uriba107/deduino/pcb/eyebrows - referance schematic/Glareshield-revA.sch

## EAGLE design pcb/eyebrows - referance schematic/Glareshield-revA.sch (2015-08-18)

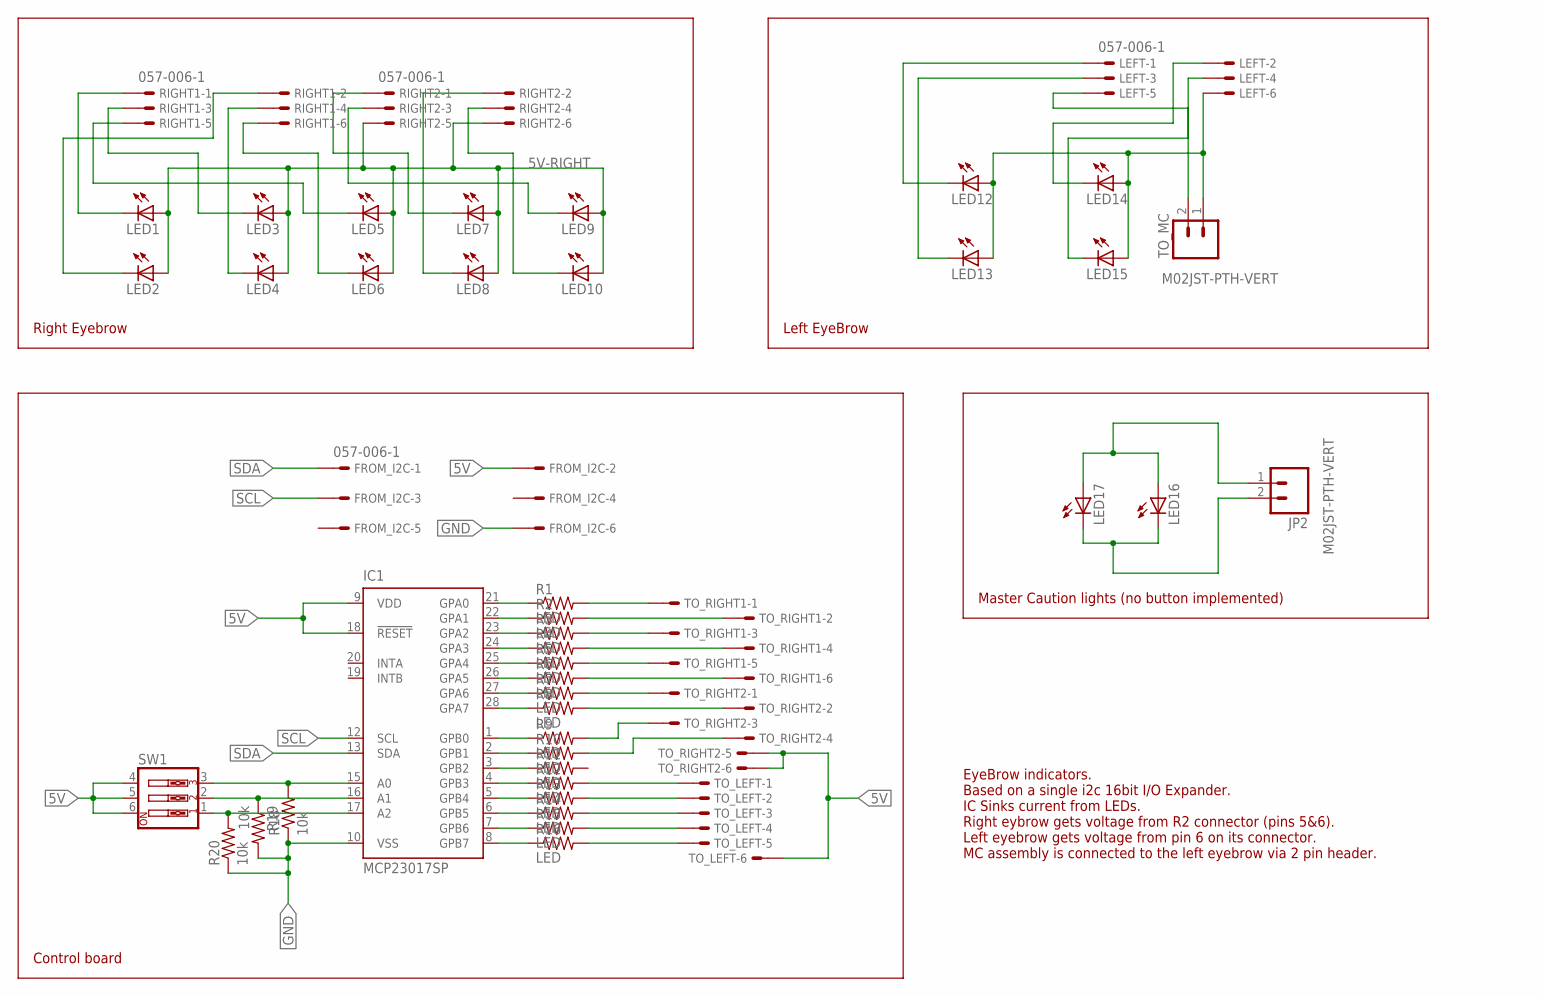
[picture p23: schematic Glareshield-revA.sch]

Parts:
FROM_I2C: 057-006-1
IC1: MCP23017SP; DIL28-3
JP2: M02JST-PTH-VERT; JST-2-PTH-VERT
LED1, LED2, LED3, LED4, LED5, LED6, LED7, LED8, LED9, LED10, LED12, LED13, LED14, LED15, LED16, LED17: LED3MM
LEFT: 057-006-1
R1, R2, R3, R4, R5, R6, R7, R8, R9, R10, R11, R12, R13, R14, R15, R16: LED; 0204/7
R18, R19, R20: 10k; 0204/7
RIGHT1, RIGHT2: 057-006-1
SW1: SW_DIP-3; EDG-03
TO_LEFT: 057-006-1
TO_MC: M02JST-PTH-VERT; JST-2-PTH-VERT
TO_RIGHT1, TO_RIGHT2: 057-006-1

Connections:
5V: FROM_I2C.2, IC1.9 (VDD), IC1.18 (!RESET), SW1.4, SW1.5, SW1.6, TO_LEFT.6, TO_RIGHT2.5, TO_RIGHT2.6
5V-LEFT: LED12.A, LED13.A, LED14.A, LED15.A, LEFT.6, TO_MC.1
5V-RIGHT: LED1.A, LED2.A, LED3.A, LED4.A, LED5.A, LED6.A, LED7.A, LED8.A, LED9.A, LED10.A, RIGHT2.5, RIGHT2.6
GND: FROM_I2C.6, IC1.10 (VSS), R18.1, R19.2, R20.1
unnamed: IC1.24 (GPA3), R4.1
unnamed: IC1.21 (GPA0), R1.1
unnamed: IC1.22 (GPA1), R2.1
unnamed: IC1.23 (GPA2), R3.1
unnamed: IC1.25 (GPA4), R5.1
unnamed: IC1.26 (GPA5), R6.1
unnamed: IC1.27 (GPA6), R7.1
unnamed: IC1.28 (GPA7), R8.1
unnamed: IC1.1 (GPB0), R9.1
unnamed: IC1.2 (GPB1), R10.1
unnamed: IC1.3 (GPB2), R11.1
unnamed: IC1.4 (GPB3), R12.1
unnamed: IC1.5 (GPB4), R13.1
unnamed: IC1.6 (GPB5), R14.1
unnamed: IC1.7 (GPB6), R15.1
unnamed: IC1.8 (GPB7), R16.1
unnamed: LED1.K (C), RIGHT1.1
unnamed: LED3.K (C), RIGHT1.3
unnamed: LED5.K (C), RIGHT1.5
unnamed: LED6.K (C), RIGHT1.6
unnamed: LED4.K (C), RIGHT1.4
unnamed: LED2.K (C), RIGHT1.2
unnamed: LED7.K (C), RIGHT2.1
unnamed: R12.2, TO_LEFT.1
unnamed: LED9.K (C), RIGHT2.3
unnamed: LED8.K (C), RIGHT2.2
unnamed: LED10.K (C), RIGHT2.4
unnamed: R1.2, TO_RIGHT1.1
unnamed: R2.2, TO_RIGHT1.2
unnamed: R3.2, TO_RIGHT1.3
unnamed: R4.2, TO_RIGHT1.4
unnamed: R5.2, TO_RIGHT1.5
unnamed: R6.2, TO_RIGHT1.6
unnamed: R7.2, TO_RIGHT2.1
unnamed: R8.2, TO_RIGHT2.2
unnamed: R10.2, TO_RIGHT2.4
unnamed: R9.2, TO_RIGHT2.3
unnamed: IC1.17 (A2), R20.2, SW1.1
unnamed: IC1.16 (A1), R19.1, SW1.2
unnamed: IC1.15 (A0), R18.2, SW1.3
unnamed: LED12.K (C), LEFT.1
unnamed: R13.2, TO_LEFT.2
unnamed: R14.2, TO_LEFT.3
unnamed: R15.2, TO_LEFT.4
unnamed: R16.2, TO_LEFT.5
unnamed: LEFT.5, TO_MC.2
unnamed: LED13.K (C), LEFT.3
unnamed: LED14.K (C), LEFT.2
unnamed: LED15.K (C), LEFT.4
unnamed: JP2.1, LED16.A, LED17.A
unnamed: JP2.2, LED16.K (C), LED17.K (C)
SCL: FROM_I2C.3, IC1.12 (SCL)
SDA: FROM_I2C.1, IC1.13 (SDA)

Notes on the sheet:
Control board
Right Eyebrow
Left EyeBrow
Master Caution lights (no button implemented)
EyeBrow indicators. Based on a single i2c 16bit I/O Expander. IC Sinks current from LEDs. Right eybrow gets voltage from R2 connector (pins 5&6). Left eyebrow gets voltage from pin 6 on its connector. MC assembly is connected to the left eyebrow via 2 pin header.
