uriba107/deduino/arduino_code/DEDunio_arduino/falconded_moon_u8g.h

/*
  Fontname: -FontForge-FalconDED_MoonVP-Book-R-Normal--16-160-72-72-P-99-WinRoman-0
  Copyright: Copyright MoonVP 2015 cloned from FalconDED wide by "alancoolhand" and "uri_ba"
  Capital A Height: 10, '1' Height: 10
  Calculated Max Values w=10 h=12 x= 5 y= 6 dx=10 dy= 0 ascent=11 len=24
  Font Bounding box     w=10 h=12 x= 0 y=-1
  Calculated Min Values           x= 0 y=-1 dx= 0 dy= 0
  Pure Font   ascent =10 descent=-1
  X Font      ascent =10 descent=-1
  Max Font    ascent =11 descent=-1
*/
//#include "u8g.h"
const u8g_fntpgm_uint8_t FalconDED_wide[3118] U8G_FONT_SECTION("FalconDED_wide") = {
  0,10,12,0,255,10,1,232,3,203,32,255,255,11,255,10,
  255,0,0,0,10,0,1,2,10,10,10,4,0,192,192,192,
  192,192,192,192,0,192,192,6,4,4,10,2,6,204,204,68,
  136,8,10,10,10,1,0,102,102,255,255,102,102,255,255,102,
  102,8,10,10,10,1,0,24,126,219,216,254,127,27,219,126,
  24,8,10,10,10,1,0,225,163,231,14,28,56,112,231,197,
  135,8,10,10,10,1,0,60,126,96,112,59,127,198,198,255,
  115,2,4,4,10,4,6,192,192,64,128,4,10,10,10,3,
  0,48,96,192,192,192,192,192,192,96,48,4,10,10,10,3,
  0,192,96,48,48,48,48,48,48,96,192,7,9,9,10,2,
  0,16,146,84,56,254,56,84,146,16,8,8,8,10,1,1,
  24,24,24,255,255,24,24,24,2,4,4,10,5,0,192,192,
  64,128,8,2,2,10,1,4,255,255,2,2,2,10,4,0,
  192,192,8,10,10,10,1,0,1,3,7,14,28,56,112,224,
  192,128,8,10,10,10,1,0,60,126,231,195,195,195,195,231,
  126,60,6,10,10,10,2,0,48,112,240,48,48,48,48,48,
  252,252,8,10,10,10,1,0,126,255,195,3,31,126,240,192,
  255,255,8,10,10,10,1,0,255,255,14,28,62,7,3,195,
  255,126,8,10,10,10,1,0,204,204,204,204,204,255,255,12,
  12,12,8,10,10,10,1,0,255,255,192,192,254,255,3,195,
  255,126,8,10,10,10,1,0,126,254,192,192,254,255,195,195,
  255,126,8,10,10,10,1,0,255,255,3,7,14,28,56,112,
  96,96,8,10,10,10,1,0,126,255,195,195,126,255,195,195,
  255,126,8,10,10,10,1,0,126,255,195,195,255,127,3,3,
  127,126,2,6,6,10,4,2,192,192,0,0,192,192,2,8,
  8,10,4,0,192,192,0,0,192,192,64,128,7,10,10,10,
  2,0,14,28,56,112,224,224,112,56,28,14,6,6,6,10,
  2,2,252,252,0,0,252,252,7,10,10,10,2,0,224,112,
  56,28,14,14,28,56,112,224,8,10,10,10,1,0,126,255,
  195,3,7,30,24,0,24,24,8,10,10,10,1,0,24,60,
  126,255,0,0,255,126,60,24,8,10,10,10,1,0,24,60,
  126,231,195,195,255,255,195,195,8,10,10,10,1,0,254,255,
  195,195,254,254,195,195,255,254,8,10,10,10,1,0,126,255,
  195,192,192,192,192,195,255,126,8,10,10,10,1,0,254,255,
  99,99,99,99,99,99,255,254,8,10,10,10,1,0,255,255,
  192,192,248,248,192,192,255,255,8,10,10,10,1,0,255,255,
  192,192,248,248,192,192,192,192,8,10,10,10,1,0,126,255,
  195,192,207,207,195,195,255,127,8,10,10,10,1,0,195,195,
  195,195,255,255,195,195,195,195,8,10,10,10,1,0,255,255,
  24,24,24,24,24,24,255,255,7,10,10,10,1,0,126,126,
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
