uriba107/deduino/arduino_code/DEDunio_arduino/falconded_full_u8g.h

/*
  Fontname: -FreeType-FalconDED-Medium-R-Normal--17-120-100-100-P-71-ISO10646-1
  Copyright: Copyright uri_ba 2014
  Capital A Height: 9, '1' Height: 9
  Calculated Max Values w= 9 h=11 x= 3 y= 5 dx= 9 dy= 0 ascent=10 len=22
  Font Bounding box     w= 9 h=11 x= 0 y=-1
  Calculated Min Values           x= 0 y=-1 dx= 0 dy= 0
  Pure Font   ascent = 9 descent=-1
  X Font      ascent = 9 descent=-1
  Max Font    ascent =10 descent=-1
*/

const u8g_fntpgm_uint8_t FalconDED_full[2190] U8G_FONT_SECTION("FalconDED_full") = {
  0,9,11,0,255,9,1,197,3,138,32,255,255,10,255,9,
  255,0,0,0,8,0,0,2,9,9,6,3,255,192,192,192,
  192,192,192,0,192,192,5,3,3,8,2,5,216,216,216,6,
  9,9,8,1,255,72,72,252,72,72,72,252,72,72,6,9,
  9,8,1,255,48,120,180,176,120,52,180,120,48,6,9,9,
  8,1,255,68,172,72,16,48,32,72,212,136,6,9,9,8,
  1,255,48,120,72,48,120,204,220,248,116,1,3,3,4,2,
  5,128,128,128,4,9,9,7,2,255,48,96,192,192,192,192,
  192,96,48,4,9,9,7,2,255,192,96,48,48,48,48,48,
  96,192,7,7,7,9,1,1,16,84,56,254,56,84,16,6,
  6,6,8,1,1,48,48,252,252,48,48,3,4,4,6,2,
  0,96,96,192,192,6,2,2,8,1,3,252,252,2,2,2,
  6,3,0,192,192,6,9,9,8,1,255,4,12,8,16,48,
  32,64,192,128,6,9,9,8,1,255,48,120,204,204,204,204,
  204,120,48,4,9,9,7,2,255,32,96,224,96,96,96,96,
  240,240,6,9,9,8,1,255,120,252,204,12,60,120,192,252,
  252,6,9,9,8,1,255,252,252,12,24,56,12,204,252,120,
  6,9,9,8,1,255,216,216,216,216,252,252,24,24,24,6,
  9,9,8,1,255,252,252,192,248,252,12,204,252,120,6,9,
  9,8,1,255,124,252,192,248,252,204,204,252,120,6,9,9,
  8,1,255,252,252,12,12,24,48,96,96,96,6,9,9,8,
  1,255,120,252,204,252,120,204,204,252,120,6,9,9,8,1,
  255,120,252,204,204,252,124,12,124,120,2,6,6,5,2,2,
  192,192,0,0,192,192,3,7,7,5,1,0,96,96,0,96,
  96,192,192,4,6,6,7,2,1,48,96,192,192,96,48,4,
  6,6,7,2,1,240,240,0,0,240,240,4,6,6,7,2,
  1,192,96,48,48,96,192,6,9,9,8,1,255,120,252,204,
  24,24,48,0,48,48,6,9,9,8,1,255,48,120,252,0,
  0,0,252,120,48,6,9,9,8,1,255,48,120,252,204,204,
  252,252,204,204,6,9,9,8,1,255,248,252,204,248,248,204,
  204,252,248,6,9,9,8,1,255,120,204,204,192,192,192,204,
  204,120,6,9,9,8,1,255,248,108,108,108,108,108,108,108,
  248,6,9,9,8,1,255,252,252,192,248,248,192,192,252,252,
  6,9,9,8,1,255,252,252,192,248,248,192,192,192,192,6,
  9,9,8,1,255,120,252,192,192,220,220,204,252,120,6,9,
  9,8,1,255,204,204,204,252,252,204,204,204,204,6,9,9,
  8,1,255,252,252,48,48,48,48,48,252,252,6,9,9,8,
  1,255,252,252,48,48,48,48,48,240,224,6,9,9,8,1,
  255,204,220,248,224,192,224,240,220,204,6,9,9,8,1,255,
  192,192,192,192,192,192,192,252,252,6,9,9,8,1,255,132,
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
  
