uriba107/deduino/arduino_code/DEDunio_arduino/fuelflow_u8g.h

/*
  Fontname: -FontForge-MS 33558-Book-R-Normal--26-260-72-72-P-201-ISO10646-1
  Copyright: (c) 2000 Derek Higgs
  Capital A Height: 0, '1' Height: 25
  Calculated Max Values w=19 h=26 x= 6 y= 1 dx=26 dy= 0 ascent=26 len=78
  Font Bounding box     w=20 h=26 x= 0 y= 0
  Calculated Min Values           x= 0 y= 0 dx= 0 dy= 0
  Pure Font   ascent =25 descent= 0
  X Font      ascent =25 descent= 0
  Max Font    ascent =26 descent= 0
*/
//#include "u8g.h"
const u8g_fntpgm_uint8_t fuelflow_u8g[1122] U8G_FONT_SECTION("fuelflow_u8g") = {
  0,20,26,0,0,25,2,195,3,195,32,255,0,26,0,25,
  0,0,0,0,26,0,1,255,255,255,255,255,255,255,255,255,
  255,255,255,255,255,0,0,0,26,0,1,16,26,52,19,0,
  0,7,192,15,240,31,240,63,248,60,124,120,60,120,30,112,
  30,240,30,240,14,240,14,240,15,240,15,240,15,240,15,240,
  15,240,14,240,14,120,30,120,30,124,60,60,60,63,248,31,
  248,15,240,7,192,4,25,25,18,6,1,112,240,240,240,240,
  240,240,240,240,240,240,240,240,240,240,240,240,240,240,240,240,
  240,240,240,240,15,26,52,19,0,0,3,224,15,248,31,252,
  63,252,60,30,56,30,120,30,56,30,56,30,0,62,0,124,
  0,248,1,240,7,224,15,192,15,128,30,0,62,0,60,0,
  120,0,120,0,112,0,255,252,255,254,255,254,127,254,17,26,
  78,21,0,0,31,254,0,63,254,0,63,254,0,31,254,0,
  0,124,0,0,248,0,1,240,0,1,224,0,3,224,0,7,
  240,0,7,252,0,7,254,0,2,63,0,0,15,0,0,7,
  128,0,7,128,0,3,128,224,3,128,240,3,128,240,7,128,
  248,7,128,124,31,0,63,255,0,63,254,0,15,252,0,3,
  240,0,19,26,78,22,0,0,3,128,0,3,128,0,7,128,
  0,7,128,0,7,128,0,15,0,0,15,0,0,15,0,0,
  30,0,0,30,0,0,30,0,0,60,28,0,60,60,0,60,
  60,0,56,60,0,120,60,0,120,60,0,112,60,0,255,255,
  224,255,255,224,255,255,224,0,60,0,0,60,0,0,60,0,
  0,60,0,0,28,0,16,26,52,20,0,0,63,240,127,248,
  127,248,127,224,120,0,120,0,120,0,120,0,120,0,127,224,
  127,240,127,248,124,252,48,62,0,30,0,15,0,15,0,15,
  0,15,0,15,224,30,240,62,255,252,127,248,63,240,15,192,
  17,26,78,20,0,0,0,48,0,0,248,0,1,248,0,3,
  240,0,7,192,0,7,128,0,15,0,0,31,0,0,30,0,
  0,63,224,0,63,248,0,127,254,0,127,254,0,124,31,0,
  248,15,0,240,7,128,240,7,128,240,7,128,240,7,128,240,
  7,128,120,15,0,124,31,0,63,254,0,63,254,0,31,248,
  0,3,224,0,14,26,52,18,0,0,127,252,255,252,255,252,
  127,252,0,60,0,56,0,120,0,120,0,112,0,240,0,240,
  0,224,1,224,1,224,1,192,3,192,3,192,3,192,7,128,
  7,128,7,128,15,0,15,0,15,0,14,0,14,0,15,26,
  52,18,0,0,7,192,31,240,63,248,127,252,120,60,240,30,
  240,30,240,30,240,30,240,28,120,60,127,252,63,248,63,248,
  127,252,120,60,240,28,240,30,240,30,240,30,240,30,120,60,
  127,252,63,248,31,240,7,192,17,26,78,21,0,0,7,224,
  0,15,248,0,63,254,0,63,254,0,124,31,0,120,15,128,
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
